nathan5x-zz/ArcReactor-Gauntlet/CircuitLayouts/CircuitLayout_1.JPG

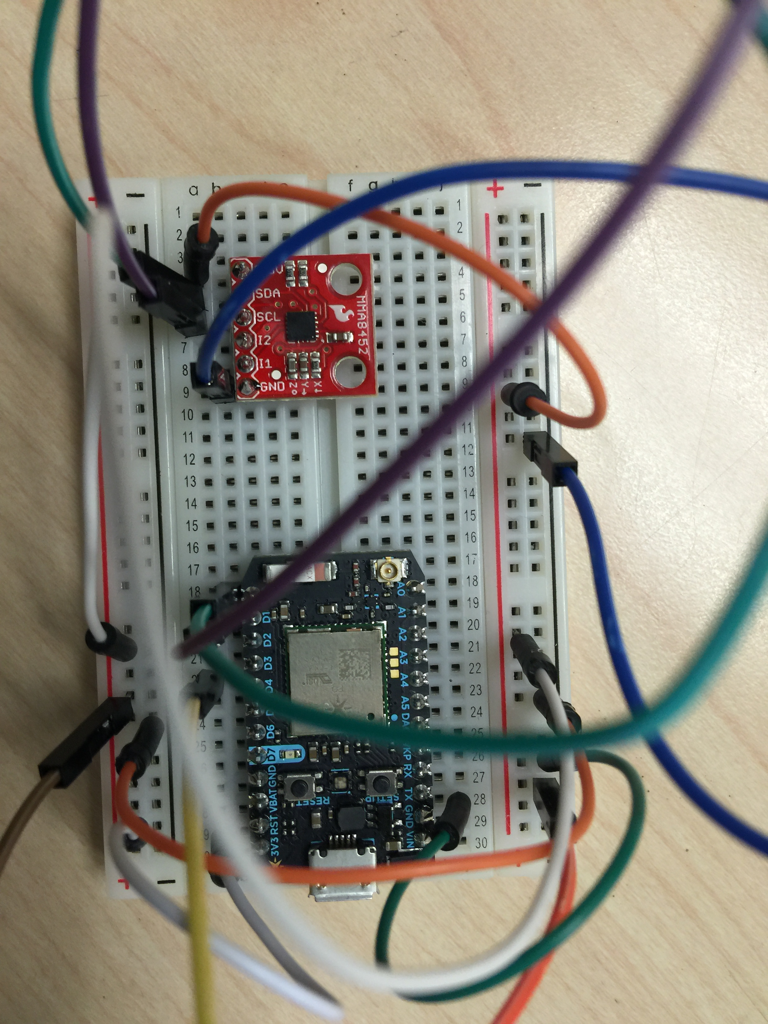
CircuitLayouts/CircuitLayout_1.JPG
