nathan5x-zz/ArcReactor-Gauntlet/CircuitLayouts/CircuitLayout_2.JPG

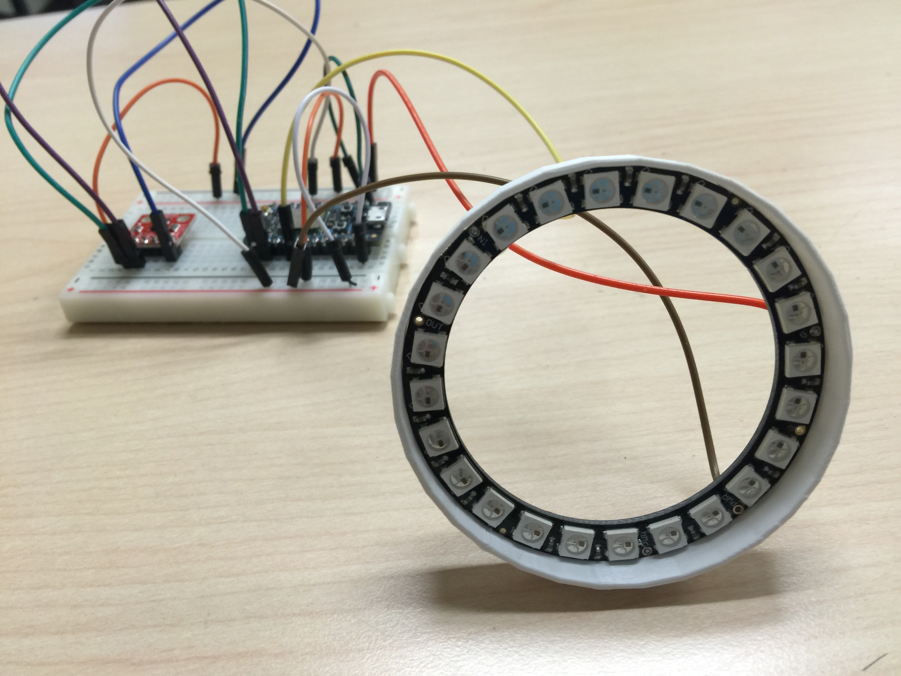
CircuitLayouts/CircuitLayout_2.JPG
