nathan5x-zz/ArcReactor-Gauntlet/CircuitLayouts/CircuitLayout_3.JPG

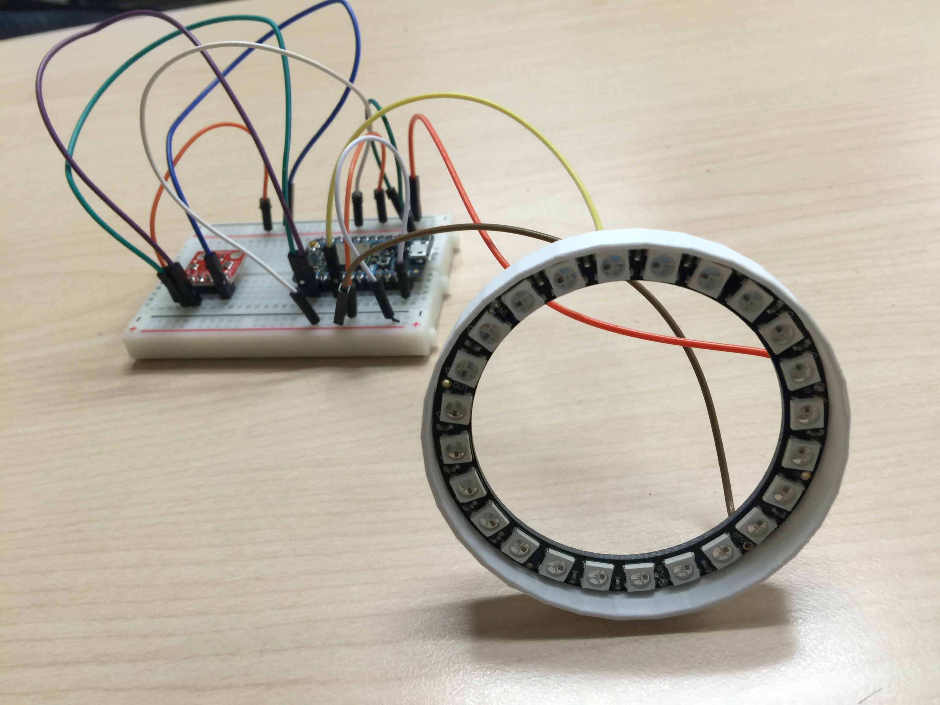
CircuitLayouts/CircuitLayout_3.JPG
