nathan5x-zz/ArcReactor-Gauntlet/CircuitLayouts/CircuitLayout_4.JPG

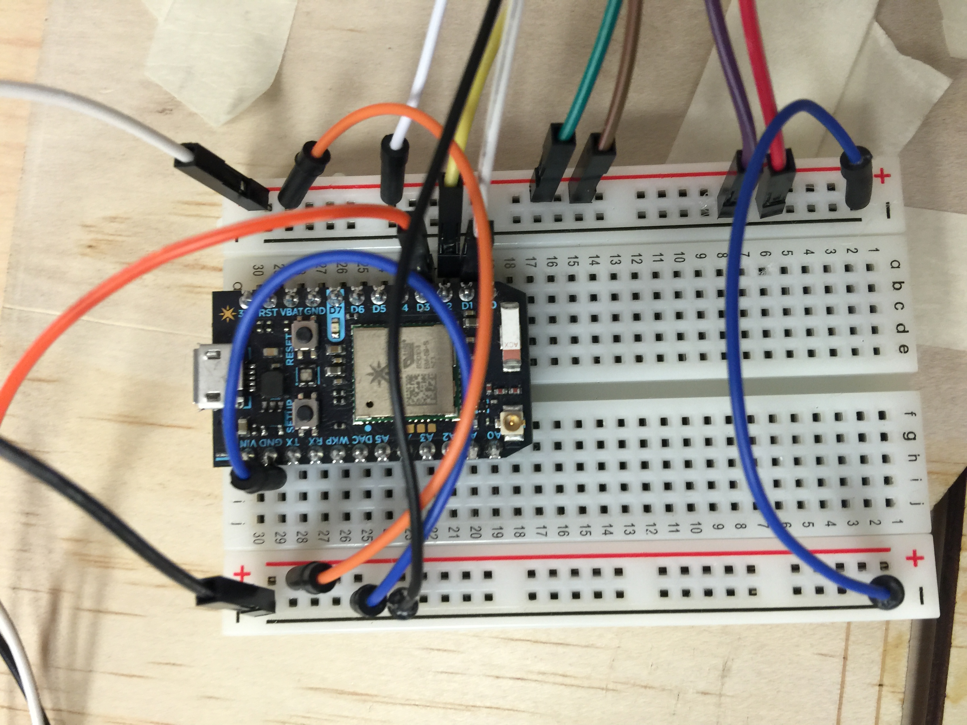
CircuitLayouts/CircuitLayout_4.JPG
