nathan5x-zz/ArcReactor-Gauntlet/CircuitLayouts/CircuitLayout_5.JPG

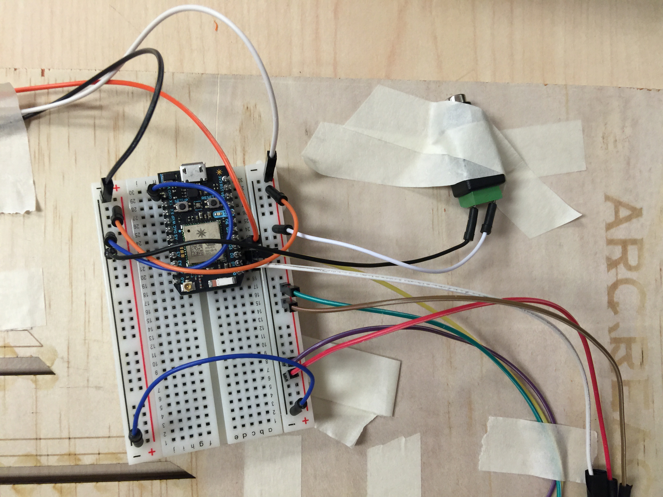
CircuitLayouts/CircuitLayout_5.JPG
