nathan5x-zz/ArcReactor-Gauntlet/CircuitLayouts/CircuitLayout_6.JPG

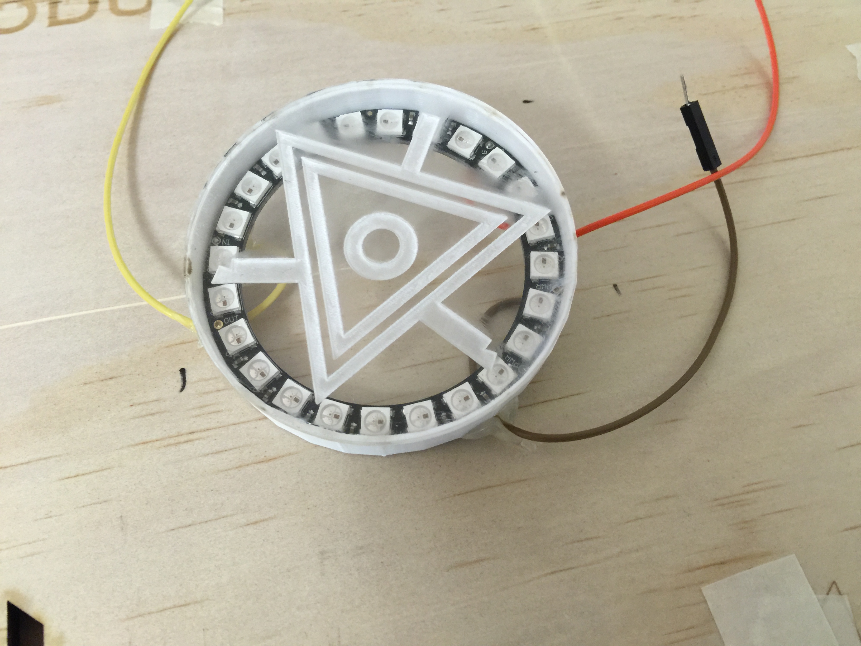
CircuitLayouts/CircuitLayout_6.JPG
