nathan5x-zz/ArcReactor-Gauntlet/CircuitLayouts/CircuitLayout_7.JPG

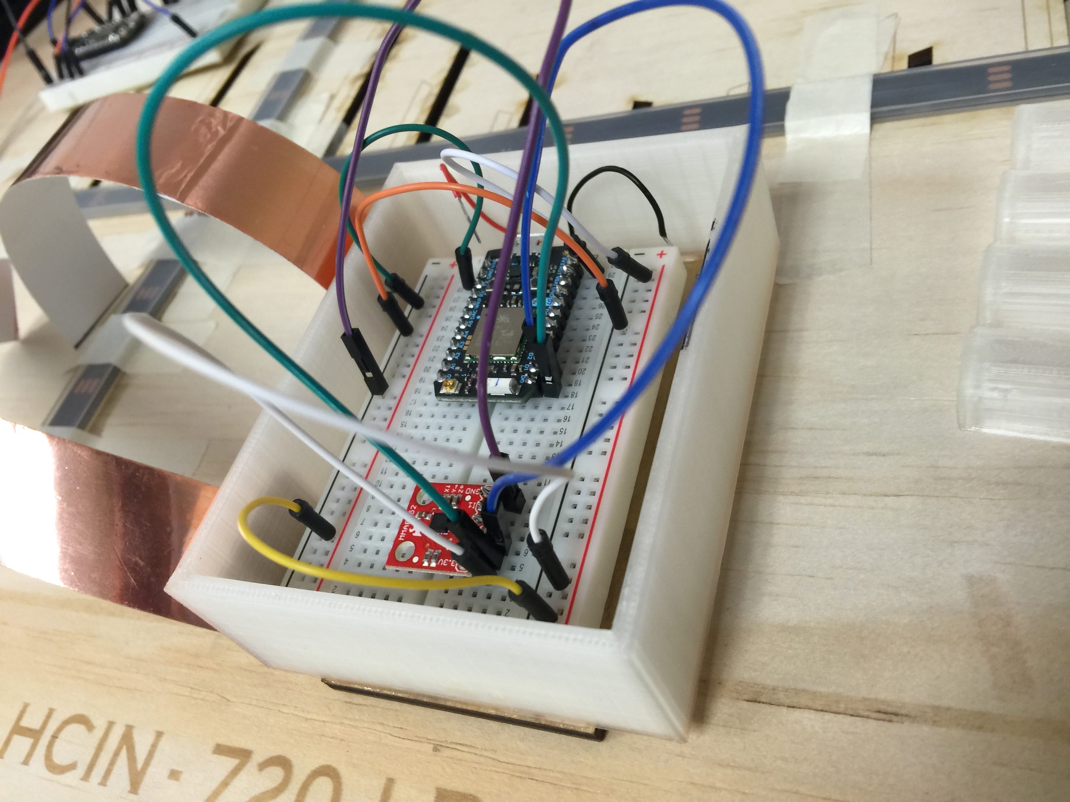
CircuitLayouts/CircuitLayout_7.JPG
