nathan5x-zz/ArcReactor-Gauntlet/CircuitLayouts/CircuitLayout_8.JPG

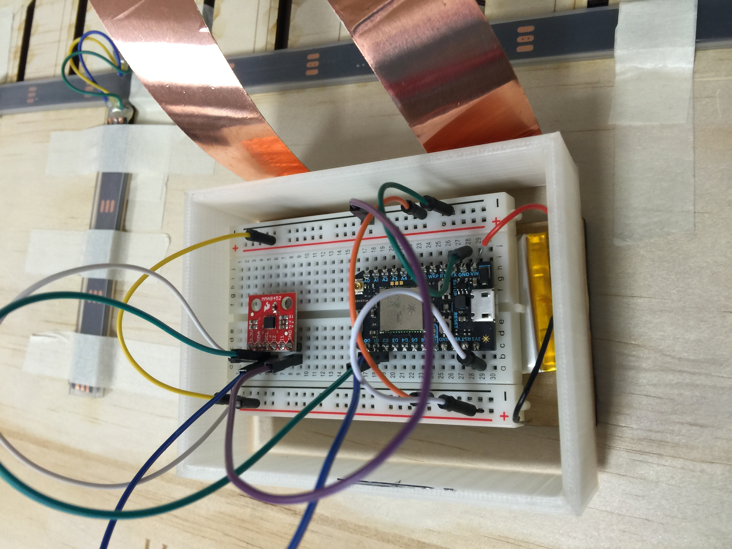
CircuitLayouts/CircuitLayout_8.JPG
