nathan5x-zz/ArcReactor-Gauntlet/CircuitLayouts/CircuitLayout_9.JPG

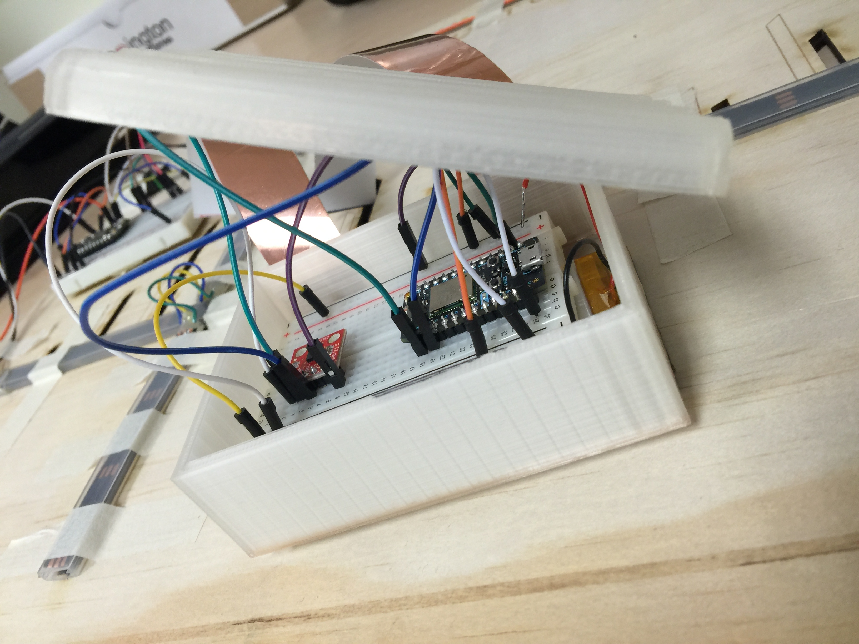
CircuitLayouts/CircuitLayout_9.JPG
