nathan5x-zz/ArcReactor-Gauntlet/PhysicalComponents/PhysicalComponent_1.JPG

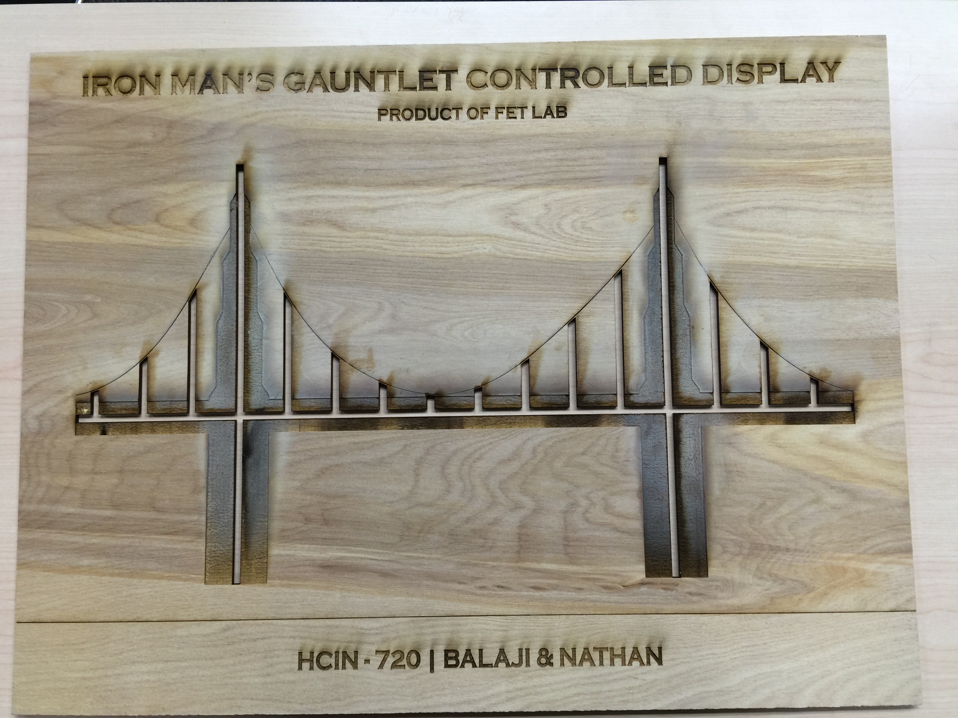
PhysicalComponents/PhysicalComponent_1.JPG
