nathan5x-zz/ArcReactor-Gauntlet/PhysicalComponents/PhysicalComponent_3.JPG

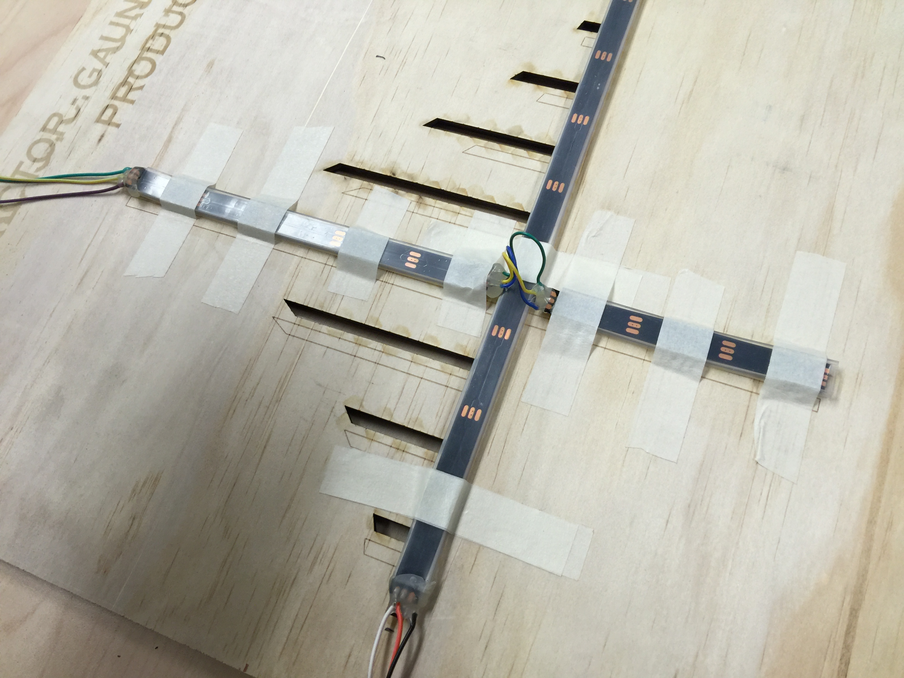
PhysicalComponents/PhysicalComponent_3.JPG
