nathan5x-zz/ArcReactor-Gauntlet/PhysicalComponents/PhysicalComponent_4.JPG

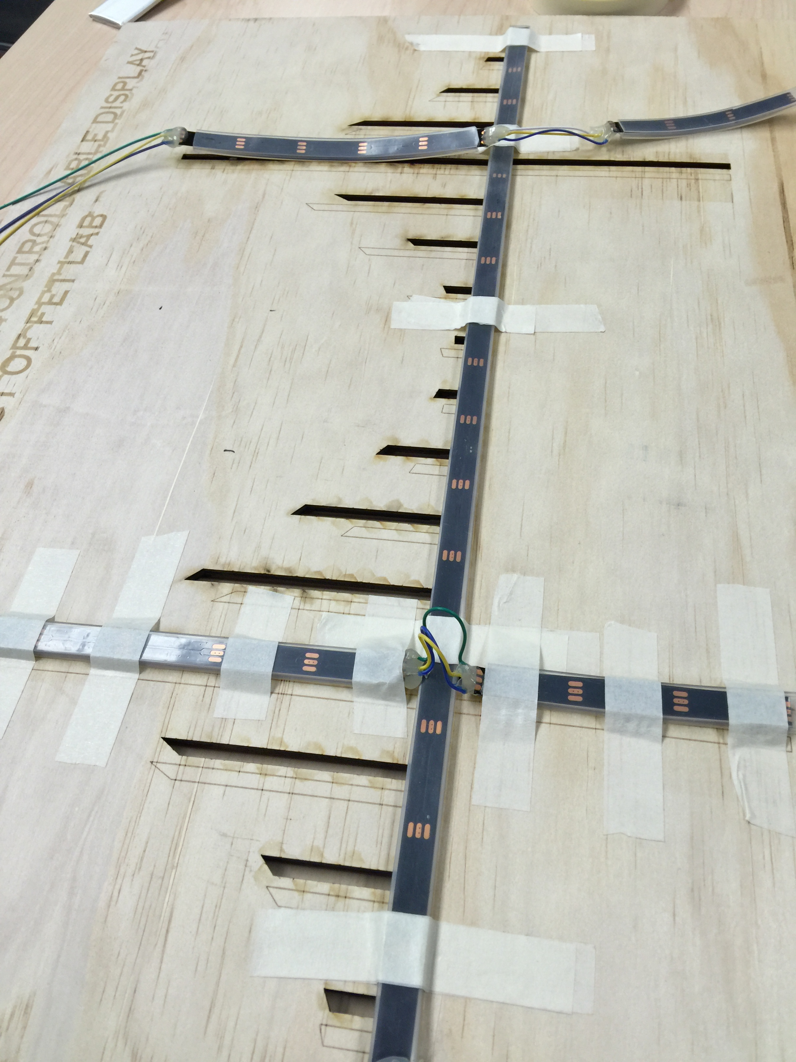
PhysicalComponents/PhysicalComponent_4.JPG
