nathan5x-zz/ArcReactor-Gauntlet/PhysicalComponents/PhysicalComponent_6.JPG

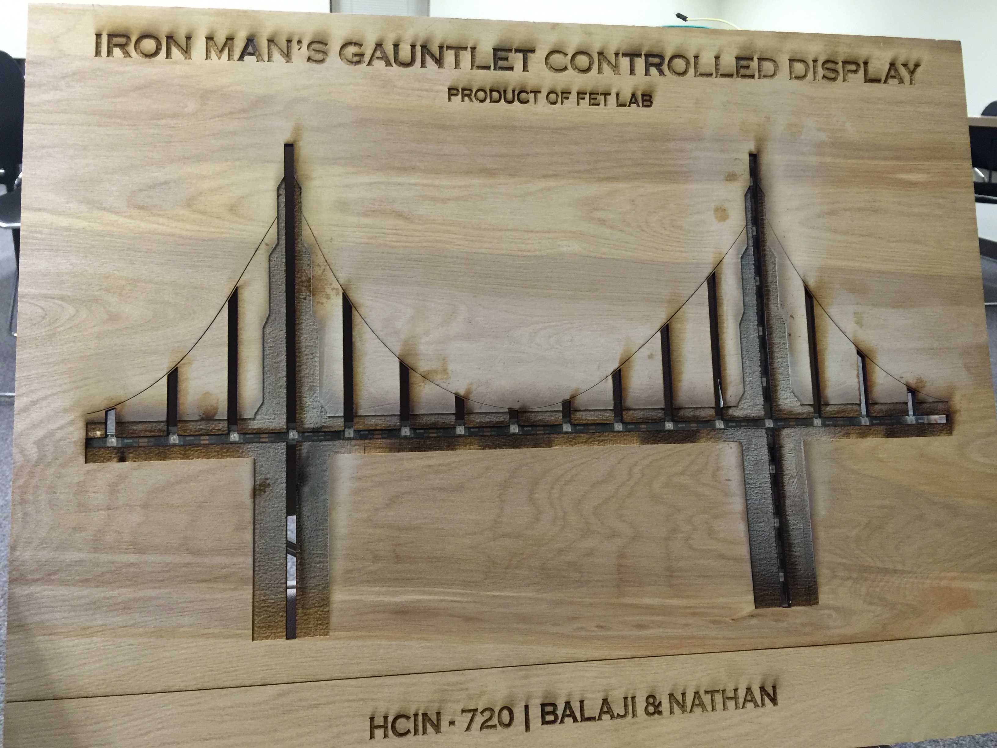
PhysicalComponents/PhysicalComponent_6.JPG
