nathan5x-zz/ArcReactor-Gauntlet/PhysicalComponents/PhysicalComponent_7.JPG

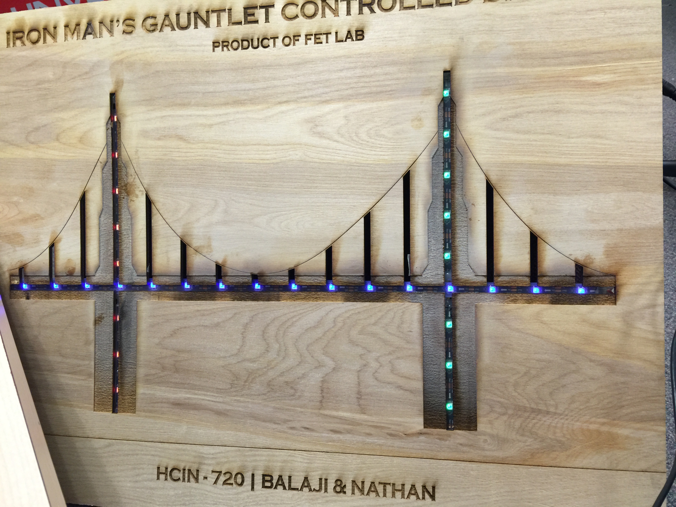
PhysicalComponents/PhysicalComponent_7.JPG
