nathan5x-zz/ArcReactor-Gauntlet/PhysicalComponents/PhysicalComponent_8.JPG

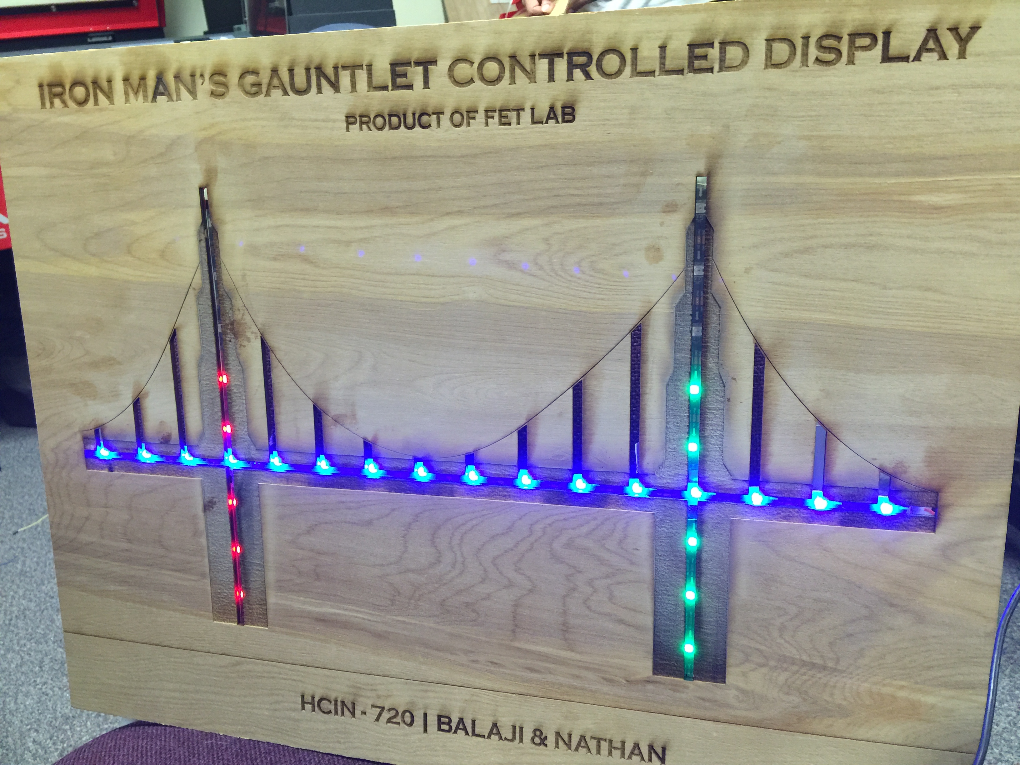
PhysicalComponents/PhysicalComponent_8.JPG
