nathan5x-zz/ArcReactor-Gauntlet/PhysicalComponents/PhysicalComponent_10.JPG

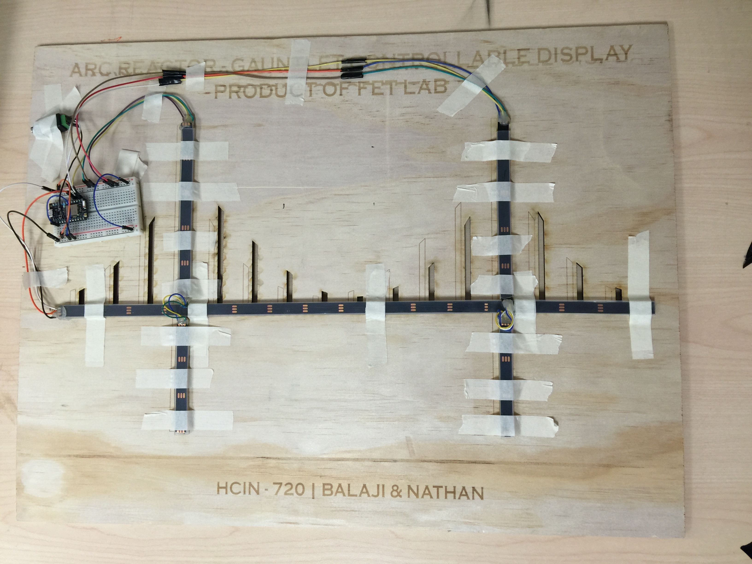
PhysicalComponents/PhysicalComponent_10.JPG
