nathan5x-zz/ArcReactor-Gauntlet/PhysicalComponents/PhysicalComponent_11.JPG

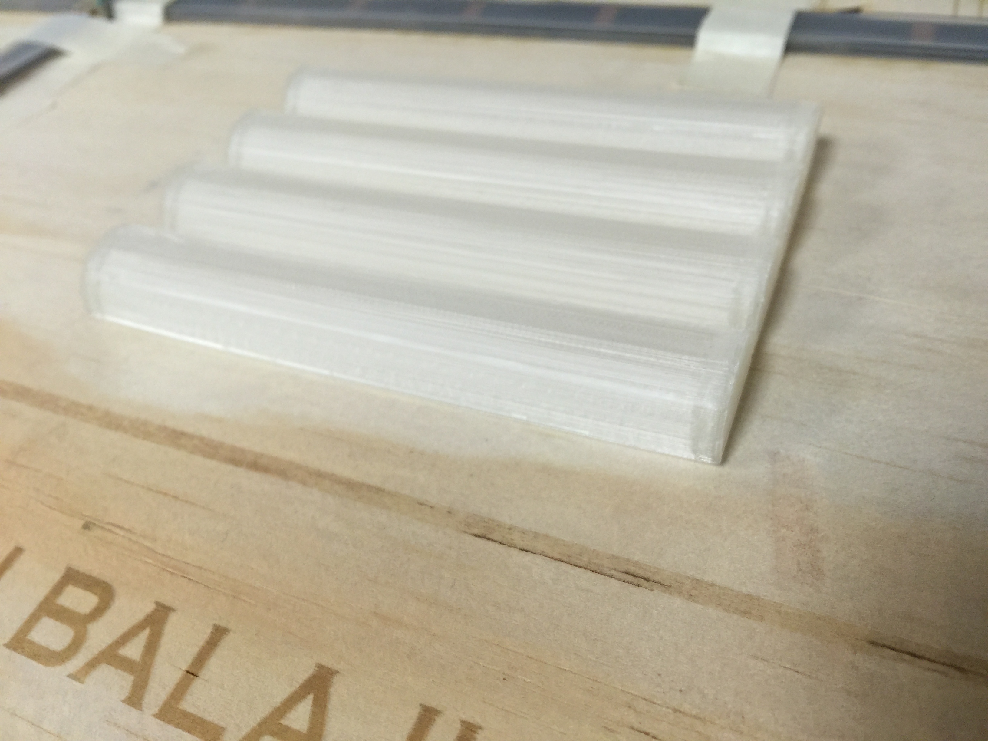
PhysicalComponents/PhysicalComponent_11.JPG
