nathan5x-zz/ArcReactor-Gauntlet/PhysicalComponents/PhysicalComponent_12.JPG

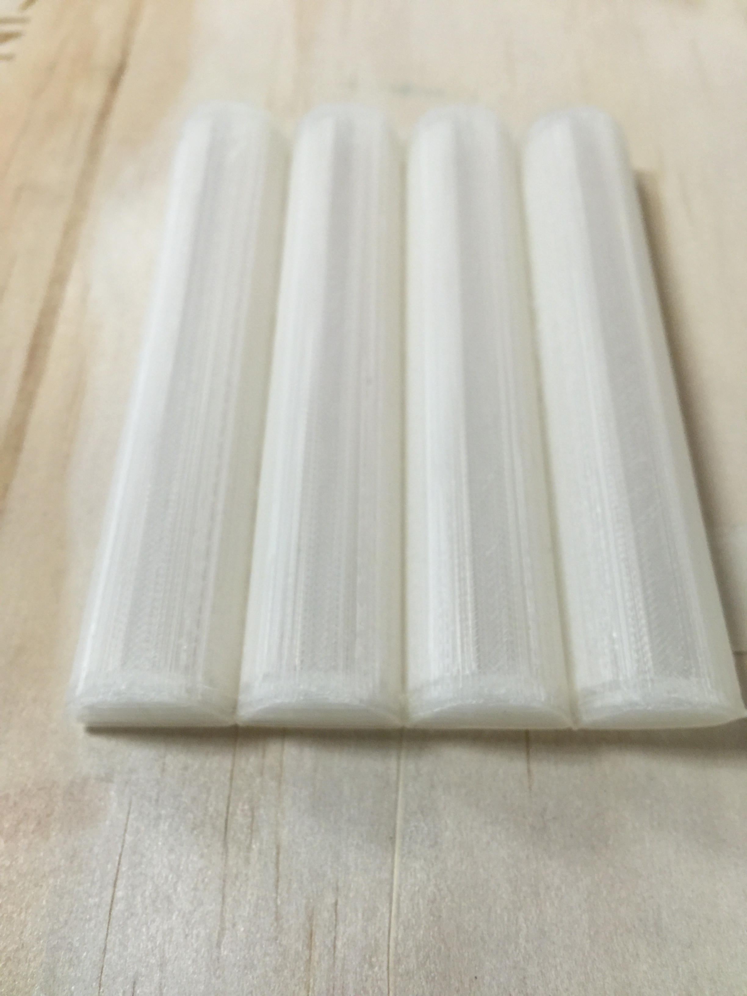
PhysicalComponents/PhysicalComponent_12.JPG
