nathan5x-zz/ArcReactor-Gauntlet/PhysicalComponents/PhysicalComponent_13.JPG

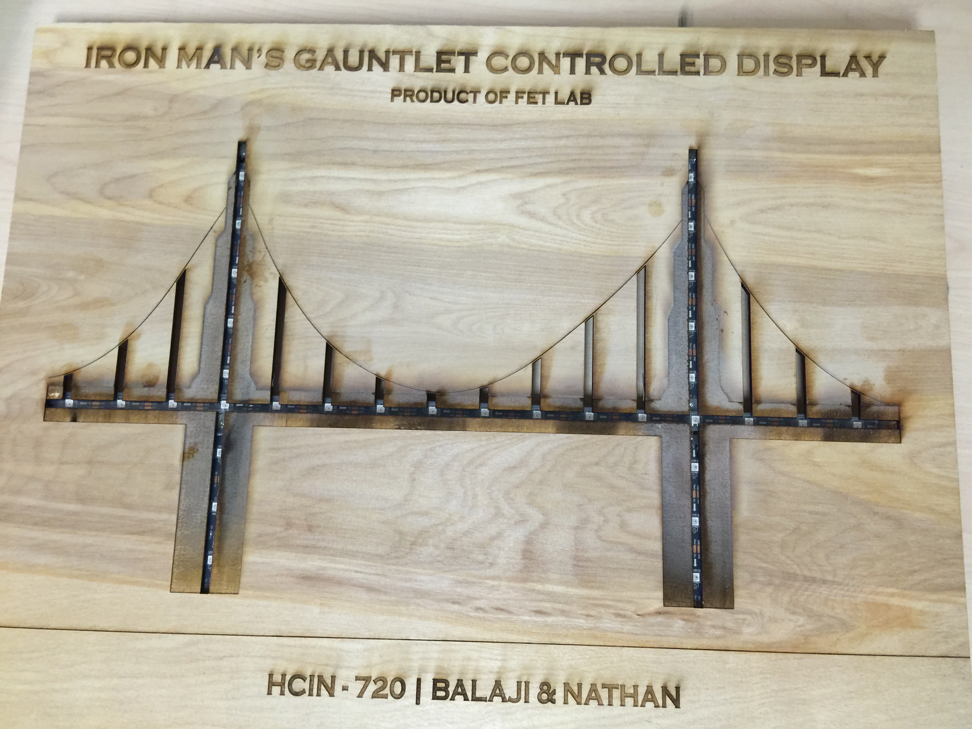
PhysicalComponents/PhysicalComponent_13.JPG
