nathan5x-zz/ArcReactor-Gauntlet/PhysicalComponents/PhysicalComponent_14.JPG

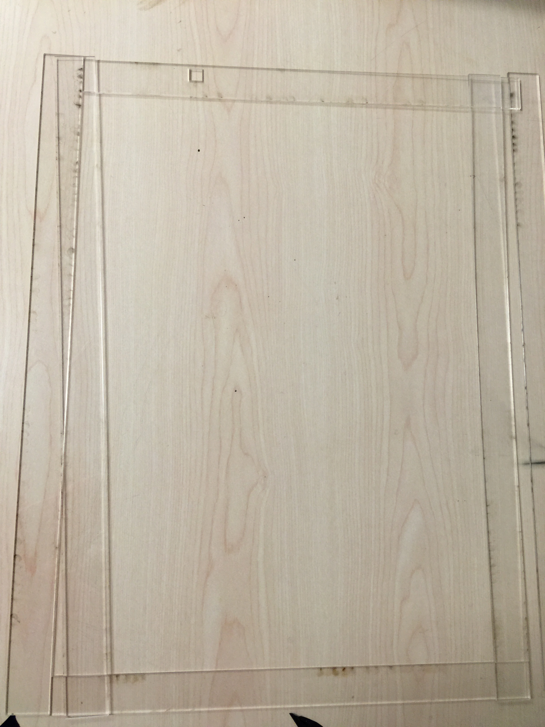
PhysicalComponents/PhysicalComponent_14.JPG
