nathan5x-zz/ArcReactor-Gauntlet/PhysicalComponents/PhysicalComponent_15.JPG

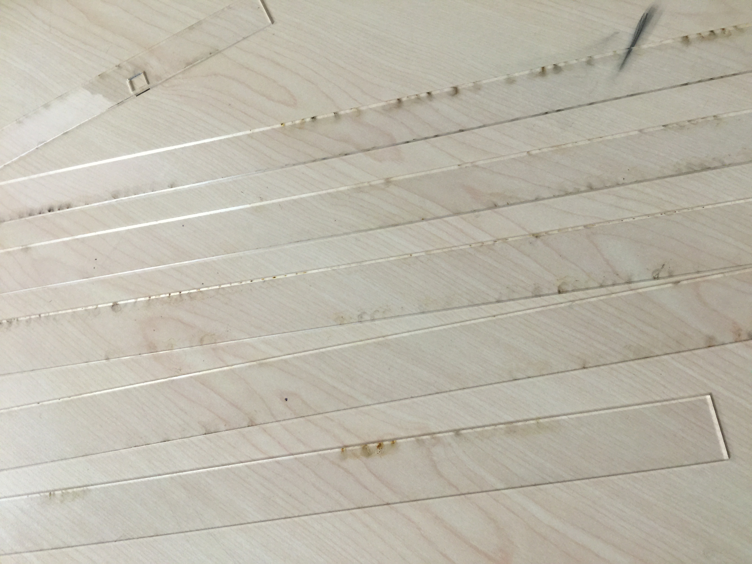
PhysicalComponents/PhysicalComponent_15.JPG
