nathan5x-zz/ArcReactor-Gauntlet/PhysicalComponents/PhysicalComponent_16.JPG

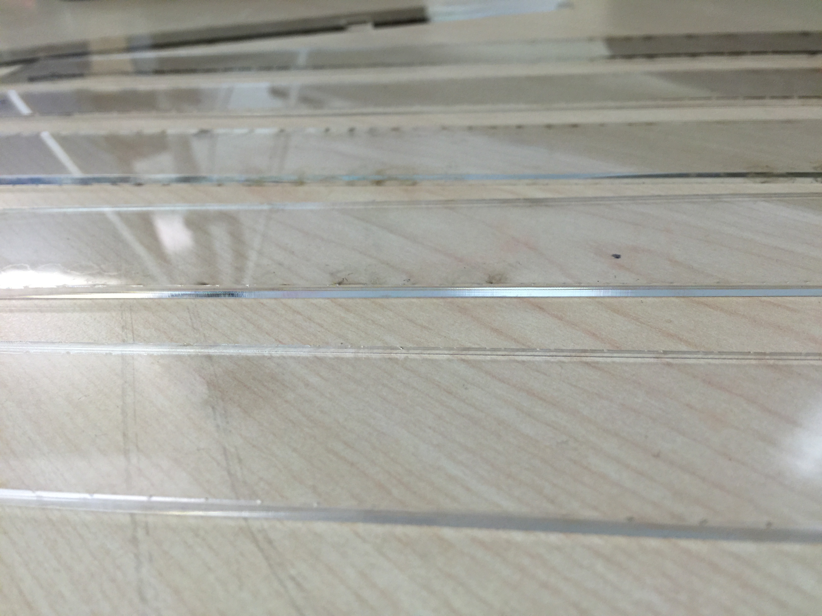
PhysicalComponents/PhysicalComponent_16.JPG
