nathan5x-zz/ArcReactor-Gauntlet/PhysicalComponents/Prototypes/Prototype_4.JPG

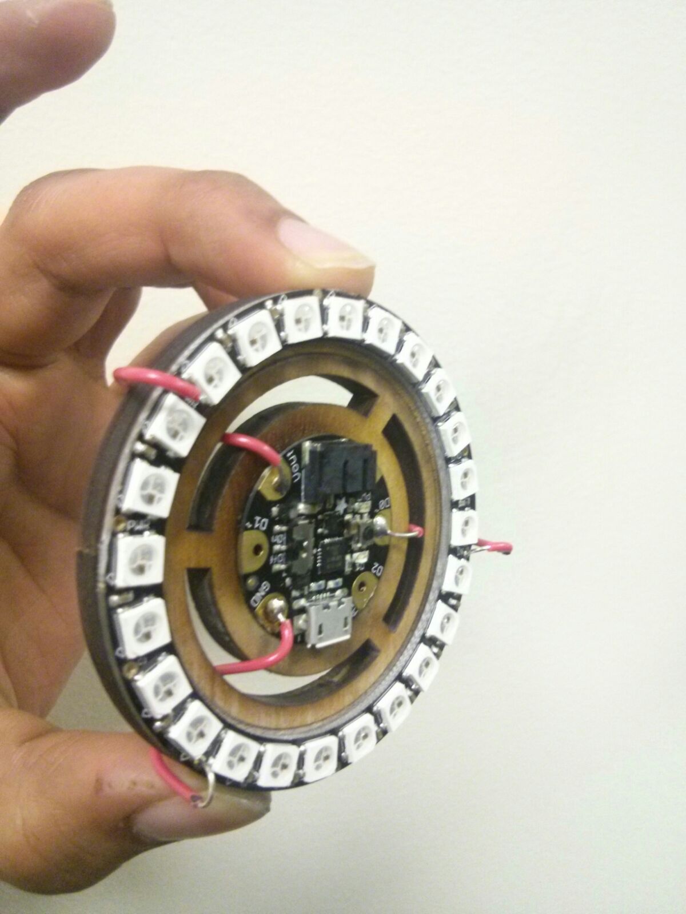
PhysicalComponents/Prototypes/Prototype_4.JPG
