nathan5x-zz/ArcReactor-Gauntlet/PhysicalComponents/Prototypes/Prototype_6.JPG

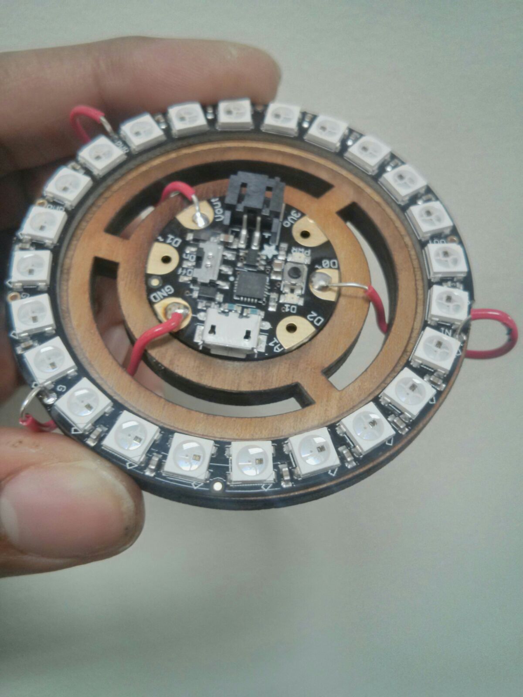
PhysicalComponents/Prototypes/Prototype_6.JPG
